ErikOSorensen/pmeter/hw/simulating_equalization_in_sensor.asc

C1: cap; 1p
C2: cap; 100n
C3: cap; 10n
L1: ind; 10n
R1: res; 50
R2: res; 51
R3: res; 470
R4: res; 1.1k
V1: voltage; SINE(0 1 10MEG); AC 1
Named nets: 0, into_sensor, RF_IN, ref_sensor
.ac dec 100 1Meg 500Meg
